JavierdeDios/ArduinoARM/media/IRL imgs/core2.jpeg

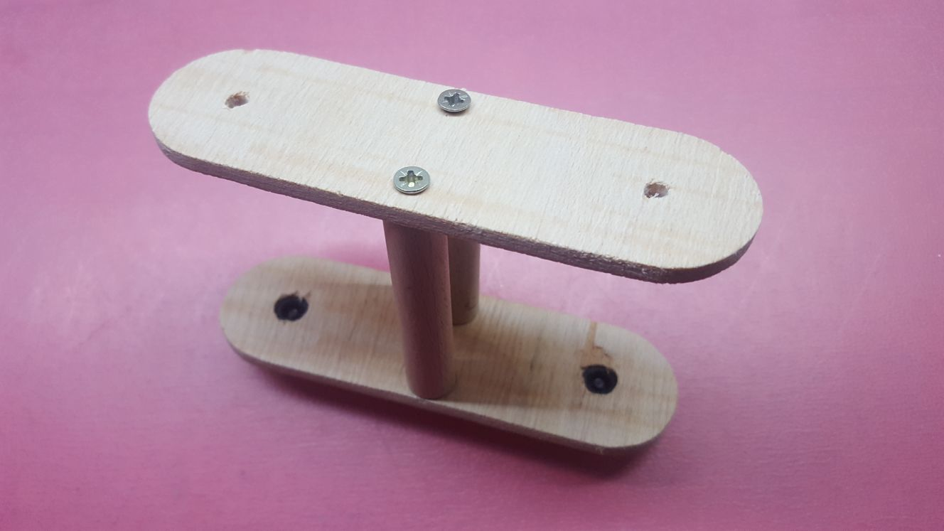
media/IRL imgs/core2.jpeg
