JavierdeDios/ArduinoARM/media/IRL imgs/side.jpeg

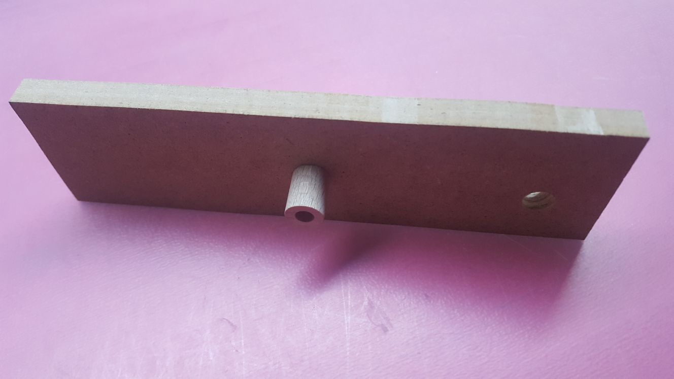
media/IRL imgs/side.jpeg
